Kybernetika-SPSE/DMP_Vagner/PROJEKTOVÁ DATA/PCB/Slave/Master_Case_1.3mf

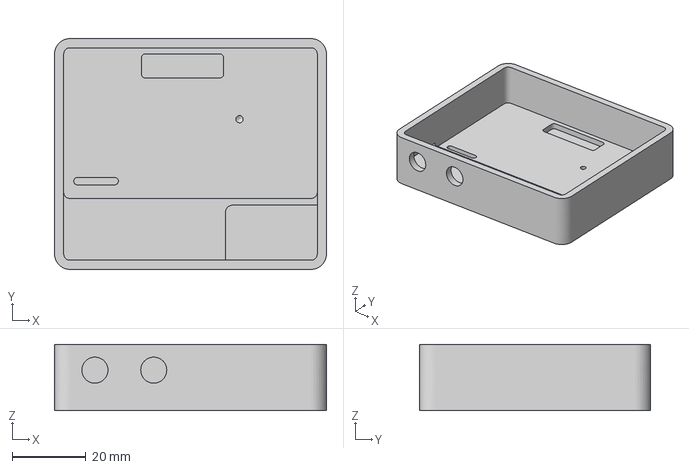
[picture p16: CAD file, 2025-01-07]
PROJEKTOVÁ DATA/PCB/Slave/Master_Case_1.3mf
74.0 x 62.8 x 18.0 mm
