Kybernetika-SPSE/DMP_Vagner/PROJEKTOVÁ DATA/PCB/Slave/Slave.step

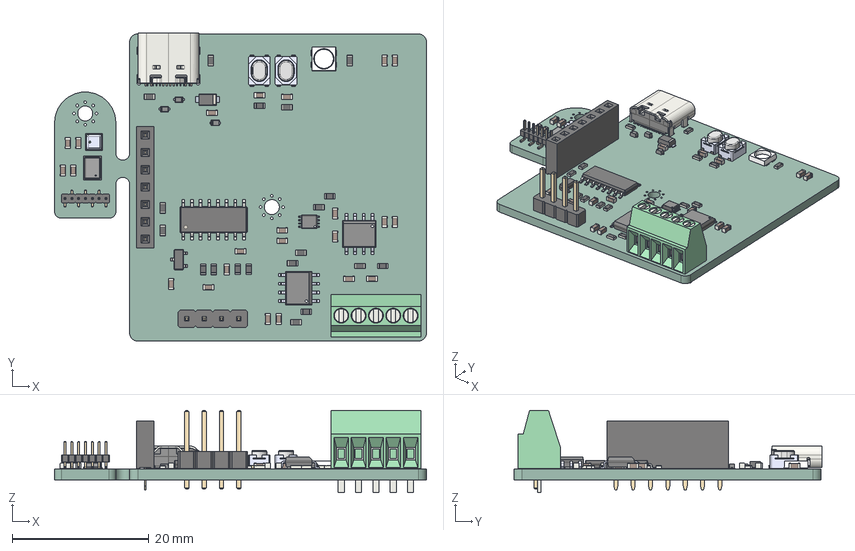
[picture p17: CAD file, 2025-01-07]
PROJEKTOVÁ DATA/PCB/Slave/Slave.step
54.5 x 45.2 x 12.0 mm
PinSocket_1x07_P254mm_Vertical
R_0603_1608Metric x 19
C_0603_1608Metric x 23
USB_C_Receptacle_16P_TopMnt_Horizontal_GCT_USB4105-xx-A
SOT_23
TXS0102DCUR
TerminalBlock_Phoenix_MPT_05_5_254_1x05_P254mm_Horizontal
PinHeader_1x04_P254mm_Vertical
InvenSense_ICS-43434-6_3.5x2.65mm
PinHeader_1x07_P100mm_Vertical_SMD_Pin1Left
D8 x 2
PTS810SJS250SMTR LFS x 2
SOP-16_3.9x9.9mm_P1.27mm
CQ assembly
LESD5D5.0CT1G x 3
SK6812MINI
BME280
Slave_PCB
